crides/zeub/firmware/drivers/is31/is31fl3741.c

/*
 * Copyright (c) 2020 The ZMK Contributors
 *
 * SPDX-License-Identifier: MIT
 */

#define DT_DRV_COMPAT issi_is31fl3741

#include <zephyr/device.h>
#include <zephyr/drivers/gpio.h>
#include <zephyr/drivers/i2c.h>
#include <zephyr/drivers/led_strip.h>
#include <zephyr/logging/log.h>
#include <zephyr/sys/math_extras.h>
#include <zephyr/sys/util.h>

LOG_MODULE_REGISTER(is31, CONFIG_ZEUB_LOG_LEVEL);

#define IS31FL3741_BUFFER_SIZE (39 * 9)
#define IS31FL3741_BUFFER_PAGE_BREAK (0xb4)

#define IS31FL3741_REG_PS (0xfd)
#define IS31FL3741_REG_PSWL (0xfe)

#define IS31FL3741_PSWL_ENABLE (0xc5)
#define IS31FL3741_PSWL_DISABLE (0x00)

#define IS31FL3741_PAGE_PWM_A (0x00)
#define IS31FL3741_PAGE_PWM_B (0x01)
#define IS31FL3741_PAGE_SCALING_A (0x02)
#define IS31FL3741_PAGE_SCALING_B (0x03)
#define IS31FL3741_PAGE_FUNCTION (0x04)

struct is31fl3741_config {
    const struct i2c_dt_spec i2c;
    const struct gpio_dt_spec sdb;
    size_t px_buffer_size;
    uint8_t gcc;
    uint8_t sws;
    uint16_t *rgb_map;
    uint8_t *gamma;
    uint8_t scaling_red;
    uint8_t scaling_blue;
    uint8_t scaling_green;
};

struct is31fl3741_data {
    uint8_t *px_buffer;
};

static int is31fl3741_reg_write(const struct device *dev, uint8_t addr, uint8_t value) {
    const struct is31fl3741_data *data = dev->data;
    const struct is31fl3741_config *config = dev->config;

    if (i2c_reg_write_byte_dt(&config->i2c, addr, value)) {
        LOG_ERR("Failed writing value %x to register address %x on device %x.", value, addr,
                config->i2c.addr);
        return -EIO;
    }

    return 0;
}

static int is31fl3741_reg_burst_write(const struct device *dev, uint8_t start_addr,
                                      const uint8_t *buffer, size_t num_bytes) {
    const struct is31fl3741_data *data = dev->data;
    const struct is31fl3741_config *config = dev->config;

    if (i2c_burst_write_dt(&config->i2c, start_addr, buffer, num_bytes)) {
        LOG_ERR("Failed burst write with starting address %x", start_addr);
        return -EIO;
    }

    return 0;
}

static int is31fl3741_set_page(const struct device *dev, uint8_t page_addr) {
    if (is31fl3741_reg_write(dev, IS31FL3741_REG_PSWL, IS31FL3741_PSWL_ENABLE)) {
        return -EIO;
    }

    if (is31fl3741_reg_write(dev, IS31FL3741_REG_PS, page_addr)) {
        return -EIO;
    }

    return 0;
}

static inline bool num_pixels_ok(const struct is31fl3741_config *config, size_t num_pixels) {
    size_t num_bytes;

    const bool overflow = size_mul_overflow(num_pixels, 3, &num_bytes);

    return !overflow && (num_bytes <= config->px_buffer_size);
}

static int is31fl3741_strip_update_channels(const struct device *dev, uint8_t *channels,
                                            size_t num_channels) {
    const struct is31fl3741_config *config = dev->config;
    struct is31fl3741_data *data = dev->data;

    if (config->px_buffer_size < num_channels) {
        return -ENOMEM;
    }

    for (int i = 0; i < num_channels; i ++) {
        data->px_buffer[config->rgb_map[i]] = config->gamma[channels[i]];
    }

    is31fl3741_set_page(dev, IS31FL3741_PAGE_PWM_A);

    int result;

    result = is31fl3741_reg_burst_write(dev, 0x00, data->px_buffer, IS31FL3741_BUFFER_PAGE_BREAK);

    if (result) {
        return result;
    }

    is31fl3741_set_page(dev, IS31FL3741_PAGE_PWM_B);

    return is31fl3741_reg_burst_write(dev, 0x00, data->px_buffer + 0xb4, config->px_buffer_size - 0xb4);
}

static int is31fl3741_strip_update_rgb(const struct device *dev, struct led_rgb *pixels,
                                       size_t num_pixels) {
    return is31fl3741_strip_update_channels(dev, (uint8_t *) pixels, num_pixels * 3);
}

/*
 * Initiates a driver instance for IS31FL3741.
 *
 * SDB is pulled high to enable chip operation followed
 * by a reset to clear out all previous values.
 *
 * Function and scaling registers are then pre-configured based on devicetree settings.
 */
int static is31fl3741_init(const struct device *dev) {
    const struct is31fl3741_config *config = dev->config;
    struct is31fl3741_data *data = dev->data;

    gpio_pin_configure_dt(&config->sdb, GPIO_OUTPUT);

    if (gpio_pin_set_dt(&config->sdb, 1)) {
        LOG_ERR("SDB pin cannot be pulled high");
        return -EIO;
    }

    // Set configuration registers
    if (is31fl3741_set_page(dev, IS31FL3741_PAGE_FUNCTION)) {
        LOG_ERR("Couldn't switch to function registers");
        return -EIO;
    }

    // Reset
    is31fl3741_reg_write(dev, 0x3f, 0xae); // Reset

    // Re-set configuration registers
    if (is31fl3741_set_page(dev, IS31FL3741_PAGE_FUNCTION)) {
        LOG_ERR("Couldn't switch to function registers");
        return -EIO;
    }

    // Configure LED driver operation mode
    is31fl3741_reg_write(dev, 0x00,
                         (config->sws << 4) | (0x01 << 3) | 0x01); // SWS, H logic, Normal operation
    is31fl3741_reg_write(dev, 0x01, config->gcc);                  // Set GCC

    // Set scaling registers
    uint8_t *px_buffer = data->px_buffer;
    const uint16_t *rgb_map = config->rgb_map;

    for (int i = 0; i < config->px_buffer_size; i += 3) {
        px_buffer[rgb_map[i]] = config->scaling_red;
        px_buffer[rgb_map[i + 1]] = config->scaling_green;
        px_buffer[rgb_map[i + 2]] = config->scaling_blue;
    }

    is31fl3741_set_page(dev, IS31FL3741_PAGE_SCALING_A);
    is31fl3741_reg_burst_write(dev, 0x00, px_buffer, 0xb4);

    is31fl3741_set_page(dev, IS31FL3741_PAGE_SCALING_B);
    is31fl3741_reg_burst_write(dev, 0x00, px_buffer + 0xb4, 0xab);

    // Re-initialize px_buffer to prevent any scaling values from being sent
    // to PWM registers during normal operation.
    for (size_t i = 0; i < config->px_buffer_size; ++i) {
        px_buffer[i] = 0;
    }

    return 0;
}

static const struct led_strip_driver_api is31fl3741_api = {
    .update_rgb = is31fl3741_strip_update_rgb,
    .update_channels = is31fl3741_strip_update_channels,
};

#define IS31FL3741_GCC(idx)                                                                        \
    (DT_INST_PROP(idx, r_ext) * DT_INST_PROP(idx, led_max_current) * 256 * 256) / (383 * 255)

#define IS31FL3741_DEVICE(idx)                                                                     \
                                                                                                   \
    static uint8_t is31fl3741_##idx##_px_buffer[IS31FL3741_BUFFER_SIZE];                           \
                                                                                                   \
    static struct is31fl3741_data is31fl3741_##idx##_data = {                                      \
        .px_buffer = is31fl3741_##idx##_px_buffer,                                                 \
    };                                                                                             \
                                                                                                   \
    static uint16_t is31fl3741_##idx##_rgb_map[IS31FL3741_BUFFER_SIZE] = DT_INST_PROP(idx, map);   \
                                                                                                   \
    static uint8_t is31fl3741_##idx##_gamma[] = DT_INST_PROP(idx, gamma);                          \
                                                                                                   \
    static const struct is31fl3741_config is31fl3741_##idx##_config = {                            \
        .i2c = I2C_DT_SPEC_GET(DT_DRV_INST(idx)),                                                  \
        .sdb = GPIO_DT_SPEC_GET(DT_DRV_INST(idx), sdb_gpios),                                      \
        .px_buffer_size = IS31FL3741_BUFFER_SIZE,                                                  \
        .gcc = IS31FL3741_GCC(idx),                                                                \
        .sws = DT_INST_PROP(idx, sw_setting),                                                      \
        .rgb_map = is31fl3741_##idx##_rgb_map,                                                     \
        .gamma = is31fl3741_##idx##_gamma,                                                         \
        .scaling_red = DT_INST_PROP(idx, red_scaling),                                             \
        .scaling_green = DT_INST_PROP(idx, green_scaling),                                         \
        .scaling_blue = DT_INST_PROP(idx, blue_scaling),                                           \
    };                                                                                             \
                                                                                                   \
    DEVICE_DT_INST_DEFINE(idx, &is31fl3741_init, NULL, &is31fl3741_##idx##_data,                   \
                          &is31fl3741_##idx##_config, POST_KERNEL, CONFIG_LED_STRIP_INIT_PRIORITY, \
                          &is31fl3741_api);

DT_INST_FOREACH_STATUS_OKAY(IS31FL3741_DEVICE);
