crides/zeub/firmware/drivers/battery/battery_common.c

/*
 * Copyright (c) 2021 The ZMK Contributors
 *
 * SPDX-License-Identifier: MIT
 */

#include <errno.h>
#include <zephyr/drivers/sensor.h>

#include "battery_common.h"

int battery_channel_get(const struct battery_value *value, enum sensor_channel chan,
                        struct sensor_value *val_out) {
    switch (chan) {
    case SENSOR_CHAN_GAUGE_VOLTAGE:
        val_out->val1 = value->millivolts / 1000;
        val_out->val2 = (value->millivolts % 1000) * 1000U;
        break;

    case SENSOR_CHAN_GAUGE_STATE_OF_CHARGE:
        val_out->val1 = value->state_of_charge;
        val_out->val2 = 0;
        break;

    default:
        return -ENOTSUP;
    }

    return 0;
}

uint8_t lithium_ion_mv_to_pct(int16_t bat_mv) {
    // Simple linear approximation of a battery based off adafruit's discharge graph:
    // https://learn.adafruit.com/li-ion-and-lipoly-batteries/voltages

    if (bat_mv >= 4200) {
        return 100;
    } else if (bat_mv >= 3800) {
        return (bat_mv - 3800) / 10 + 60;
    } else if (bat_mv >= 3700) {
        return (bat_mv - 3700) * 2 / 5 + 20;
    } else if (bat_mv >= 3500) {
        return (bat_mv - 3500) / 20 + 10;
    } else {
        return (bat_mv - 3000) / 50;
    }
}
