crides/zeub/firmware/include/pixel_font.h

static const uint8_t pixel_font[] = {
    0x1F, 0x11, 0x1F,
    0x09, 0x1F, 0x01,
    0x17, 0x15, 0x17,
    0x15, 0x15, 0x1F,
    0x1C, 0x04, 0x1F,
    0x1D, 0x15, 0x17,
    0x1F, 0x15, 0x17,
    0x10, 0x10, 0x1F,
    0x1F, 0x15, 0x1F,
    0x1D, 0x15, 0x1F,   // 9
    0x01,               // . 
    0x05,               // :
    0x10, 0x00, 0x1F, 0x11, 0x11, // oC
};

struct font_info {
    uint8_t start;
    uint8_t len;
    char *s;
};

static const struct font_info font_info[] = {
    {0, 3, "0"},
    {3, 3, "1"},
    {6, 3, "2"},
    {9, 3, "3"},
    {12, 3, "4"},
    {15, 3, "5"},
    {18, 3, "6"},
    {21, 3, "7"},
    {24, 3, "8"},
    {27, 3, "9"},
    {30, 1, "."},
    {31, 1, ":"},
    {32, 5, "oC"},
};
